ZanzyTHEbar/Smart-Air-Filter-Project/Arduino ESP32-S3 PlatformIO Build/Purbright_Esp32_PlatformIO/customname.py

Import("env")

my_flags = env.ParseFlags(env['BUILD_FLAGS'])
defines = {k: v for (k, v) in my_flags.get("CPPDEFINES")}
# print(defines)

env.Replace(PROGNAME="firmware_Purbright%s" % defines.get("VERSION"))
